prtana/power-relay-switcher/firmware/power-relay-switcher/Core/Inc/relays.h

/*
 * relays.h
 *
 *  Created on: Jan 11, 2022
 *      Author: Priit Tänav
 */

#ifndef INC_RELAYS_H_
#define INC_RELAYS_H_

#include "stm32l0xx_hal.h"

typedef enum
{
	RELAY_CLOSED = 0,
	RELAY_OPEN
} RelayState;

typedef struct
{
	GPIO_TypeDef *GPIO;
	uint32_t 	  Pin;
} RelayTypedef;

void SetRelayState (const RelayTypedef *relay, RelayState state);
RelayState GetRelayState (const RelayTypedef *relay);

#endif /* INC_RELAYS_H_ */
