prtana/power-relay-switcher/firmware/power-relay-switcher/Core/Src/relays.c

/*
 * relays.c
 *
 *  Created on: Jan 11, 2022
 *      Author: Priit Tänav
 */
#include "stm32l0xx_hal.h"
#include "main.h"
#include "relays.h"
#include "switches.h"

void SetRelayState (const RelayTypedef *relay, RelayState state)
{
	if (state == RELAY_CLOSED)
	{
		HAL_GPIO_WritePin(relay->GPIO, relay->Pin, GPIO_PIN_SET);
	}
	else if (state == RELAY_OPEN)
	{
		HAL_GPIO_WritePin(relay->GPIO, relay->Pin, GPIO_PIN_RESET);
	}
}

RelayState GetRelayState (const RelayTypedef *relay)
{
	GPIO_PinState pin_state = HAL_GPIO_ReadPin(relay->GPIO, relay->Pin);

	if (pin_state == GPIO_PIN_SET)
	{
		return RELAY_CLOSED;
	}
	else
	{
		return RELAY_OPEN;
	}
}
